devoopes/defcon26-meow/art/jpg-export/meow_v4.jpg

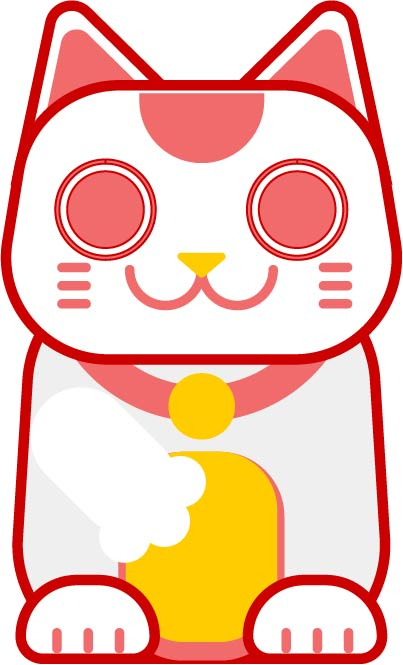
art/jpg-export/meow_v4.jpg
