devoopes/defcon26-meow/art/jpg-export/meow_v5.jpg

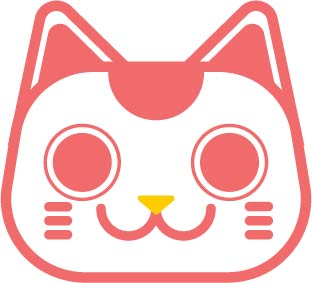
art/jpg-export/meow_v5.jpg
