devoopes/defcon26-meow/art/meow_v5_nogray_outline.png

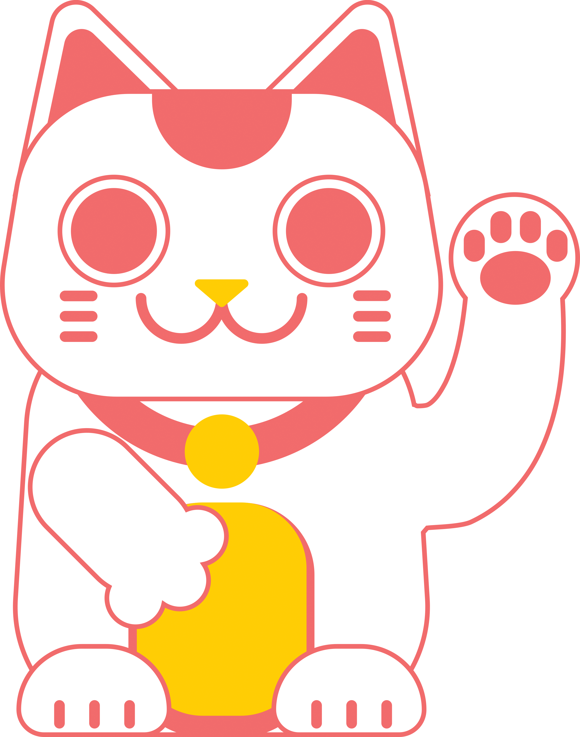
art/meow_v5_nogray_outline.png
