devoopes/defcon26-meow/art/png-export/belly.png

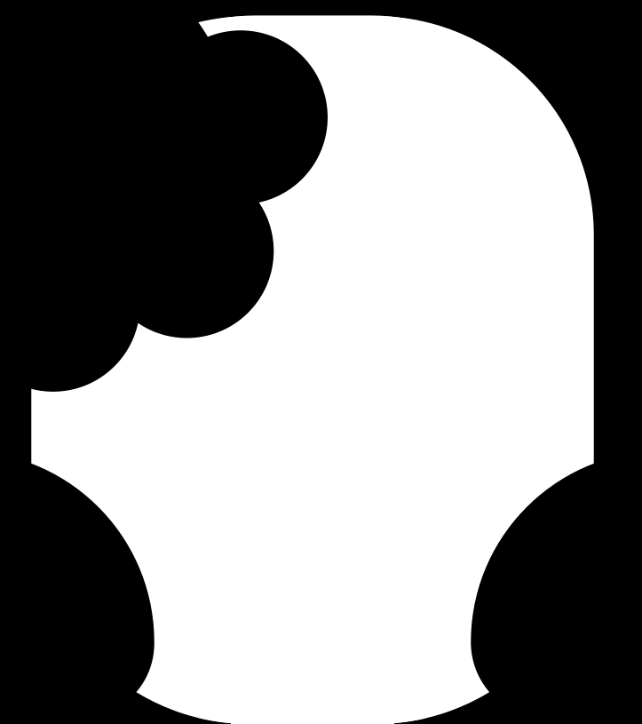
art/png-export/belly.png
