devoopes/defcon26-meow/art/png-export/belly_new.png

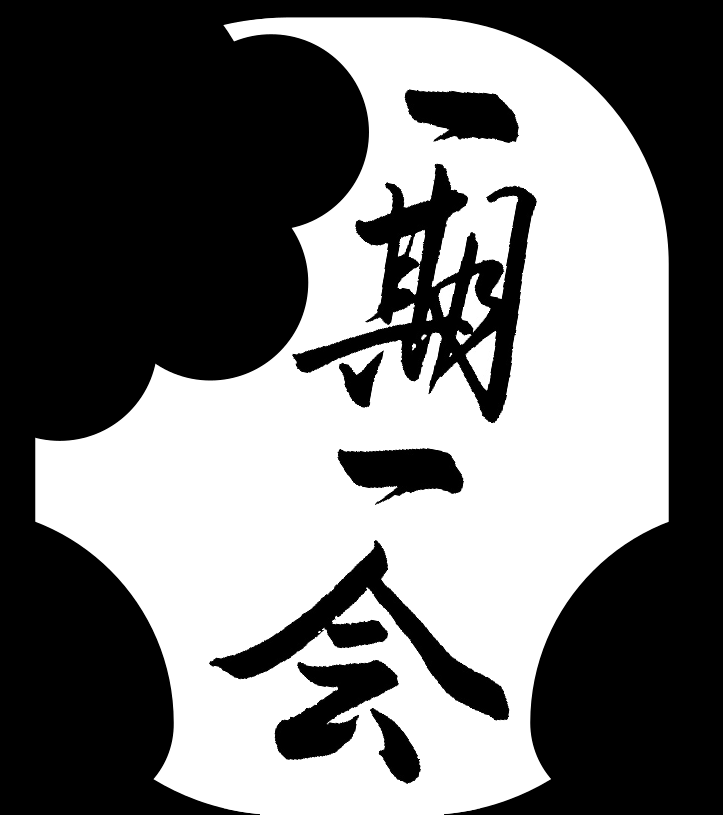
art/png-export/belly_new.png
