devoopes/defcon26-meow/art/png-export/collar.png

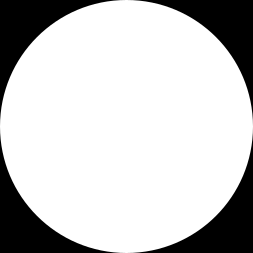
art/png-export/collar.png
