devoopes/defcon26-meow/art/png-export/meow_v4.png

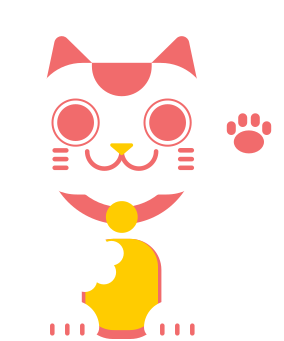
art/png-export/meow_v4.png
