devoopes/defcon26-meow/art/png-export/meow_v4_cu.png

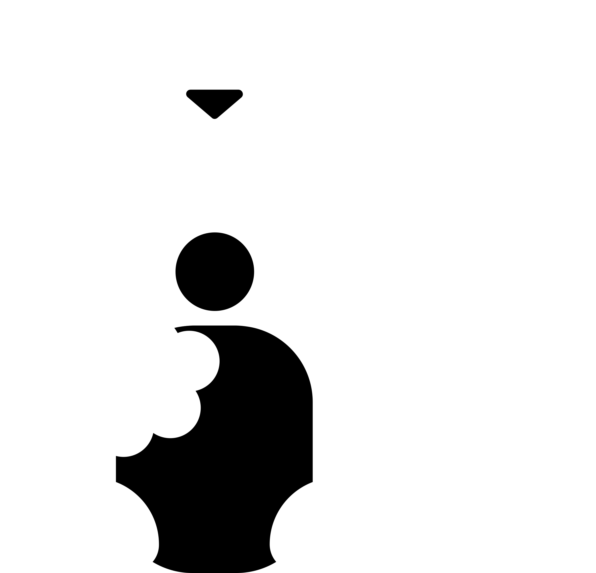
art/png-export/meow_v4_cu.png
