devoopes/defcon26-meow/art/png-export/silk-invert-cu.png

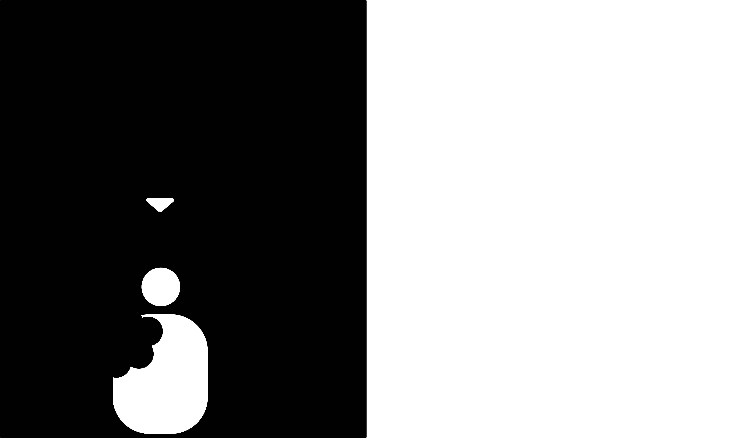
art/png-export/silk-invert-cu.png
