devoopes/defcon26-meow/art/png-export/silk-invert.png

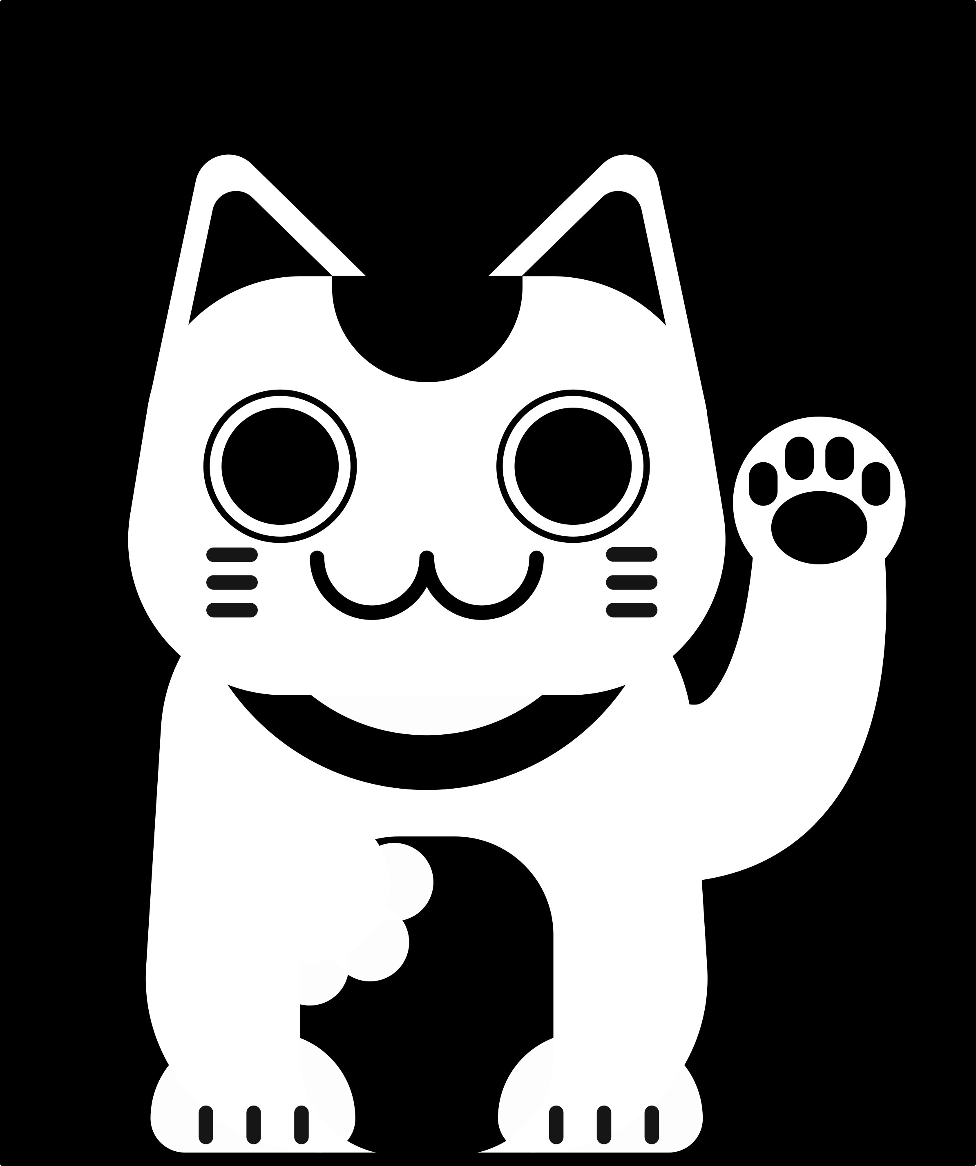
art/png-export/silk-invert.png
