devoopes/defcon26-meow/art/png-export/silk.png

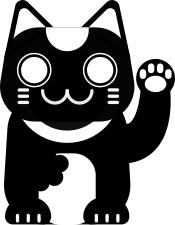
art/png-export/silk.png
