devoopes/defcon26-meow/art/rough-draft01.jpg

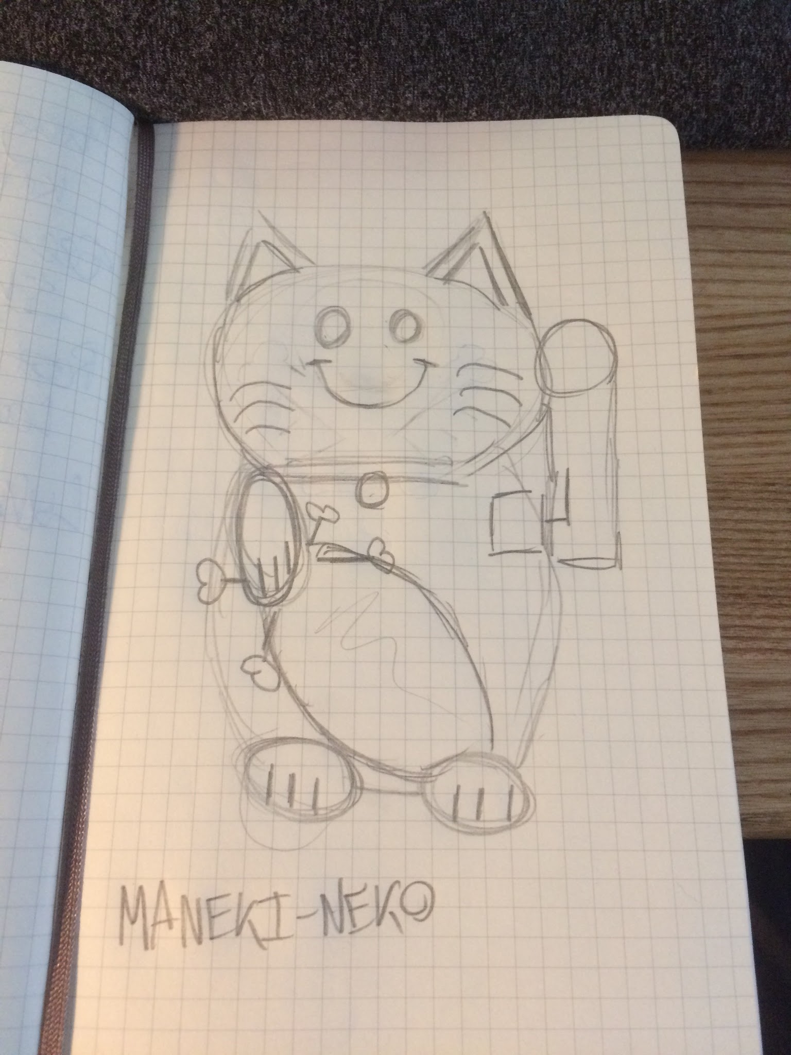
art/rough-draft01.jpg
