devoopes/defcon26-meow/art/rough-draft02.jpg

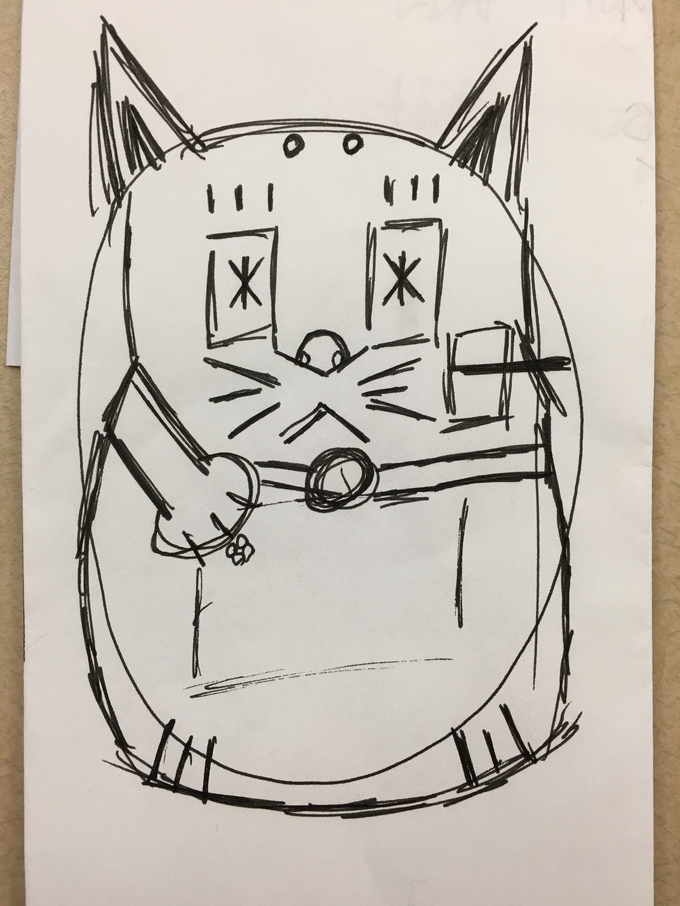
art/rough-draft02.jpg
