devoopes/defcon26-meow/pcb/eagle/art prep/meow_v4_coin_fixed.bmp

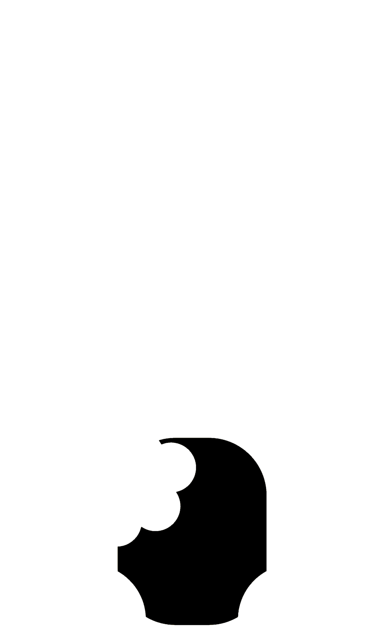
pcb/eagle/art prep/meow_v4_coin_fixed.bmp
