devoopes/defcon26-meow/pcb/eagle/art prep/meow_v4_copper.bmp

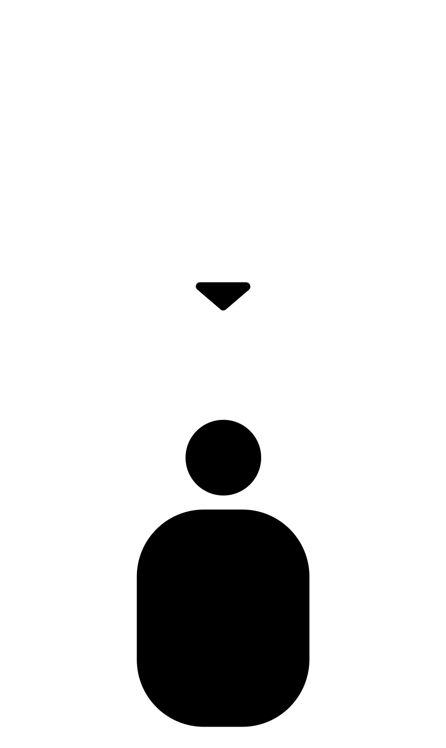
pcb/eagle/art prep/meow_v4_copper.bmp
