devoopes/defcon26-meow/pcb/eagle/art prep/meow_v4_redfill2.bmp

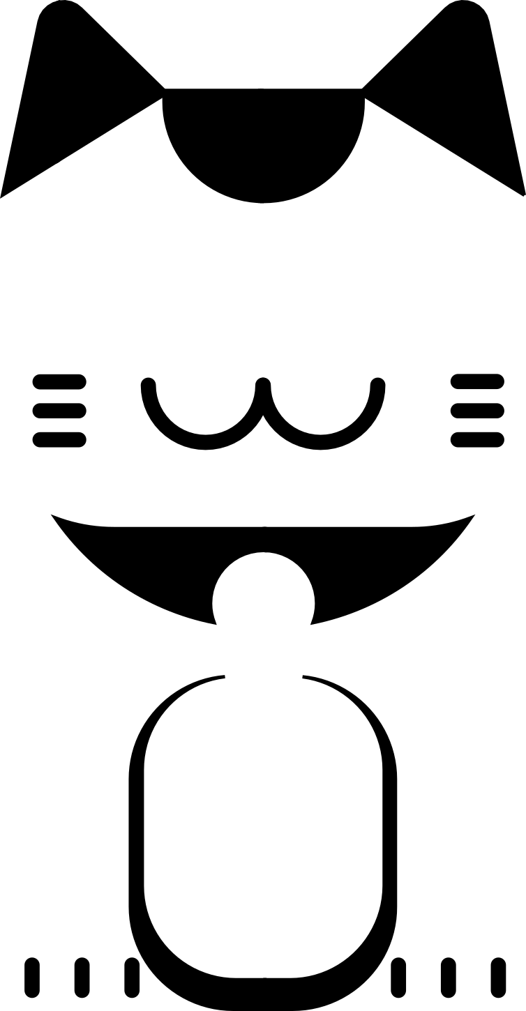
pcb/eagle/art prep/meow_v4_redfill2.bmp
