devoopes/defcon26-meow/pcb/eagle/art prep/meow_v4_stock.png

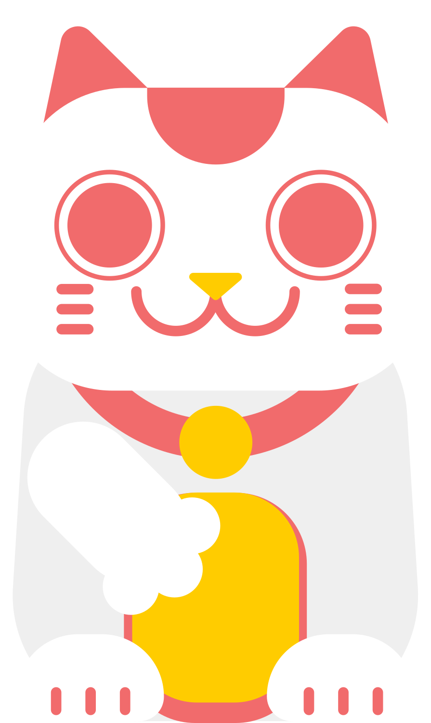
pcb/eagle/art prep/meow_v4_stock.png
