devoopes/defcon26-meow/pcb/eagle/art prep/meow_v4_stock_eyes.bmp

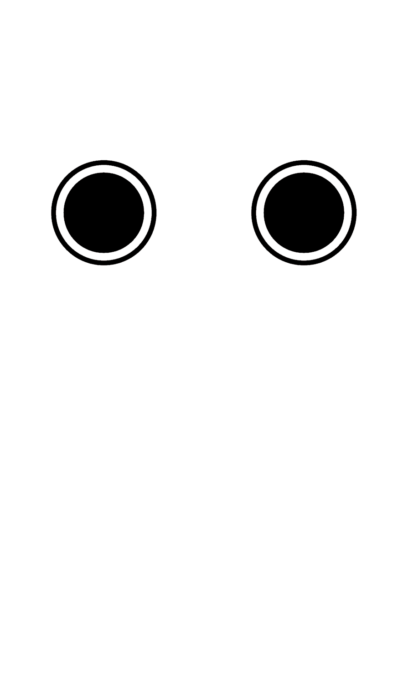
pcb/eagle/art prep/meow_v4_stock_eyes.bmp
