devoopes/defcon26-meow/art/working files/star-lg.dxf

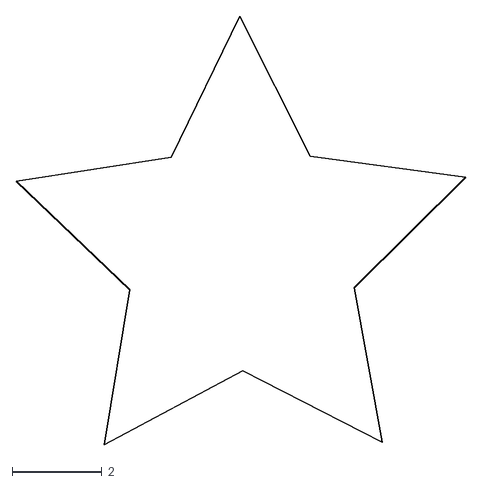
[picture p38: CAD file, 2018-07-28]
art/working files/star-lg.dxf
10.0 x 9.54
