devoopes/defcon26-meow/pcb/eagle/art prep/meow_v4_boardoutline.dxf

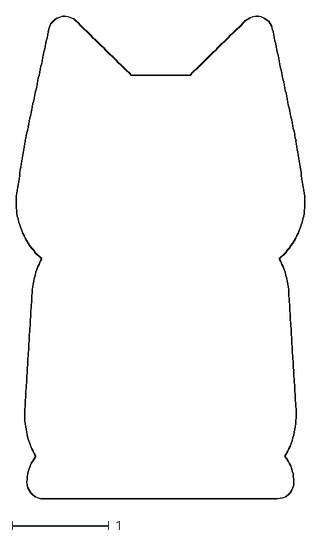
[picture p39: CAD file, 2018-06-10]
pcb/eagle/art prep/meow_v4_boardoutline.dxf
2.98 x 4.99
