devoopes/defcon26-meow/art/working files/meow_v4.dxf

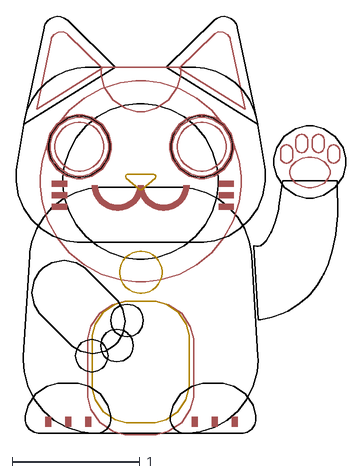
[picture p40: CAD file, 2018-07-22]
art/working files/meow_v4.dxf
2.58 x 3.27
