devoopes/defcon26-meow/art/meow_v4_mask-copy.dxf

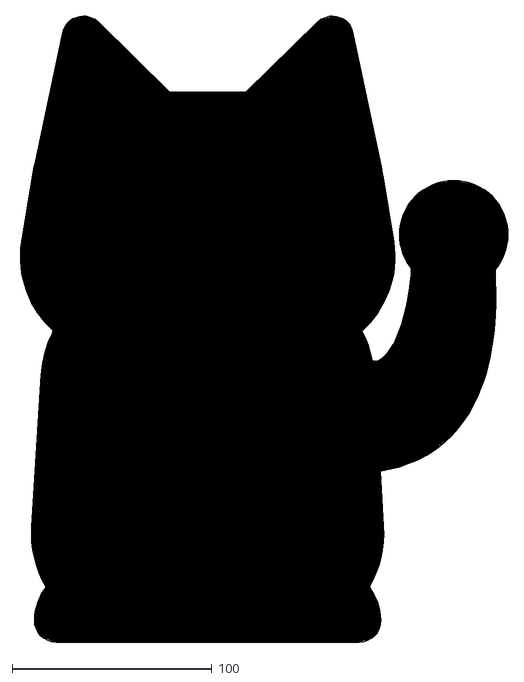
[picture p41: CAD file, 2018-07-28, an earlier design]
art/meow_v4_mask-copy.dxf
246.3 x 313.6
